mfkiwl/HF-PA-v7/datasheets/irf510-pinout-equivalent.gif

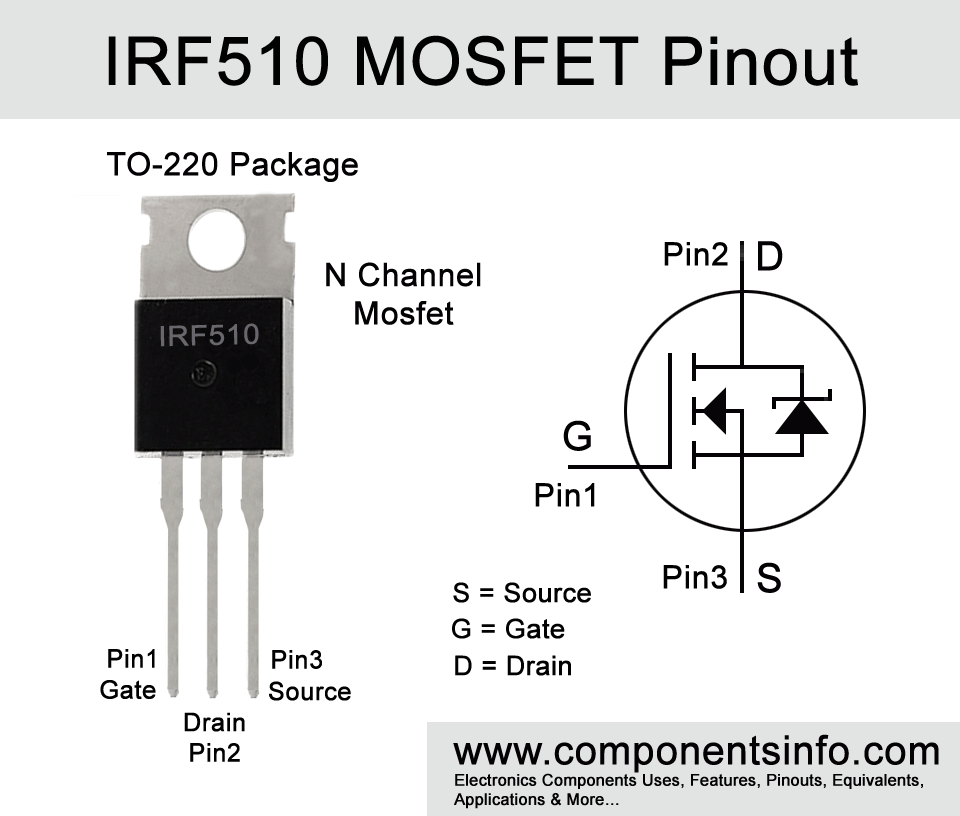
datasheets/irf510-pinout-equivalent.gif
