mfkiwl/HF-PA-v7/datasheets/rd16hhf1-pout-vs-pin.png

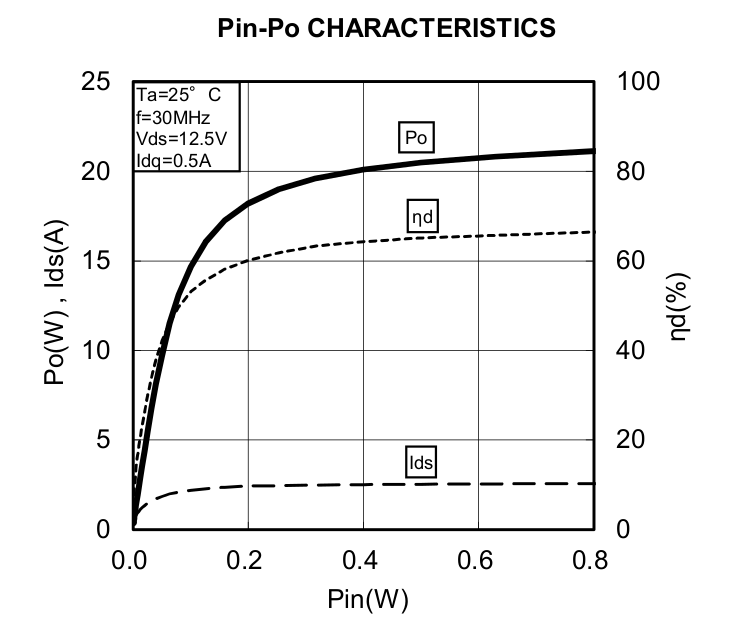
datasheets/rd16hhf1-pout-vs-pin.png
