mfkiwl/HF-PA-v7/Info/15-02-2021-11-58-602a61e1a4f83.jpeg

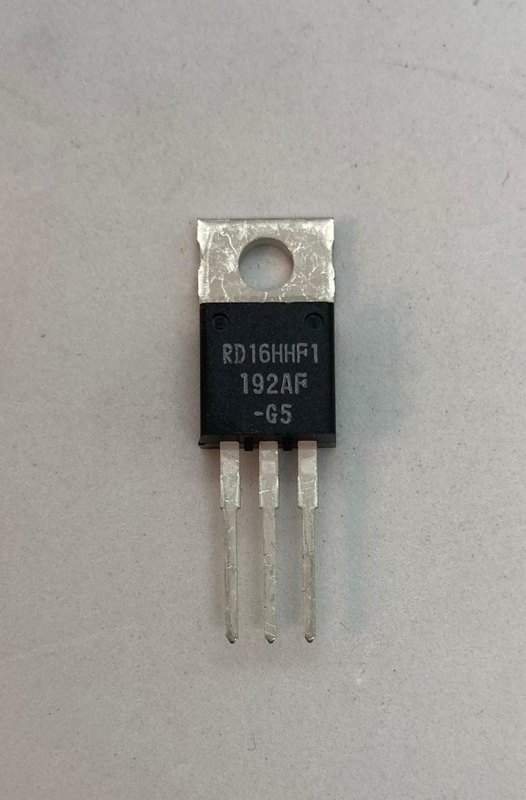
Info/15-02-2021-11-58-602a61e1a4f83.jpeg
