mfkiwl/HF-PA-v7/Info/28M5Wamp1.png

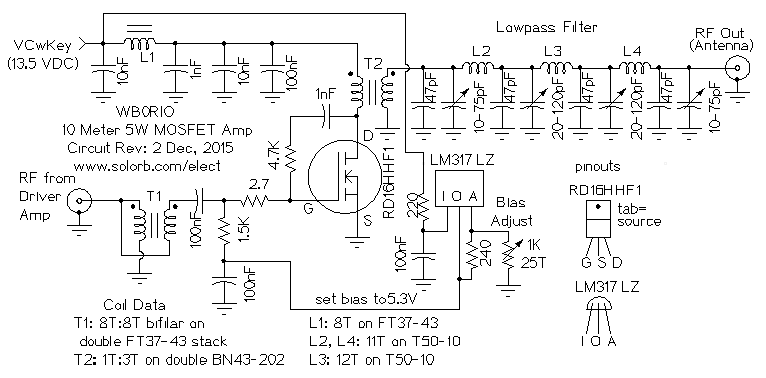
Info/28M5Wamp1.png
