mfkiwl/HF-PA-v7/Info/1367.jpg

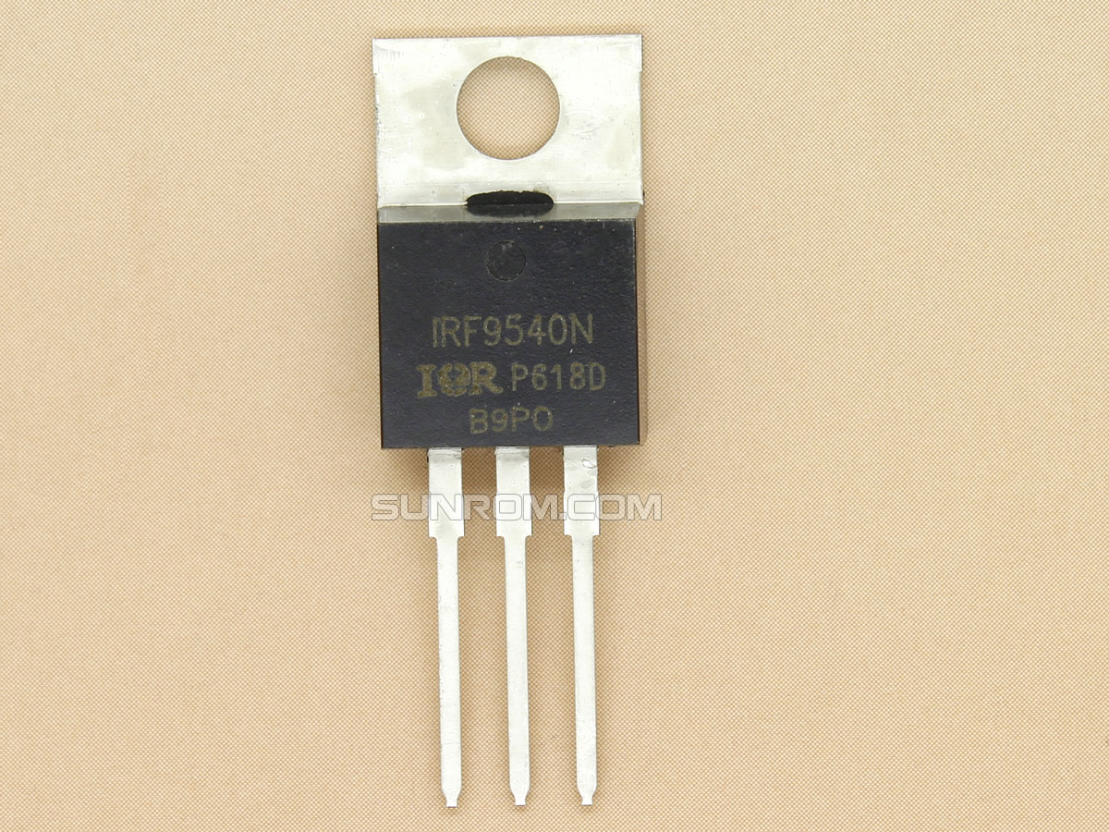
Info/1367.jpg
