mfkiwl/HF-PA-v7/Info/ MTR5B PA.png

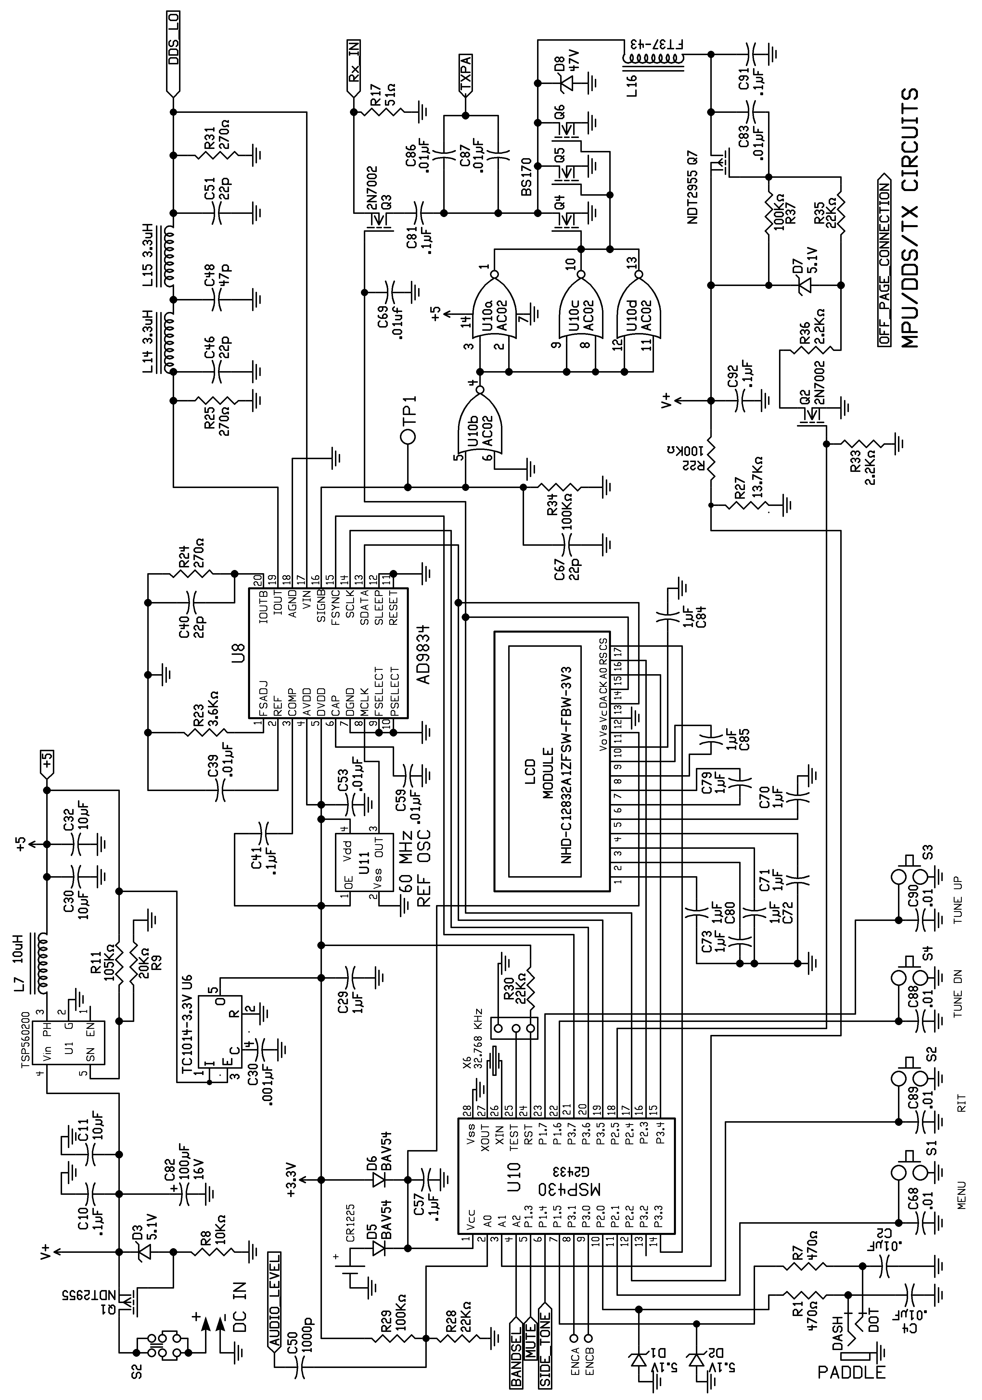
Info/ MTR5B PA.png
