mfkiwl/HF-PA-v7/Info/Hex-Inverter-As-MOSFET-Driver.png

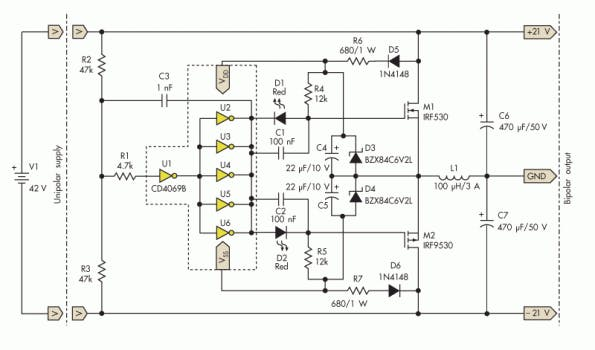
Info/Hex-Inverter-As-MOSFET-Driver.png
