mfkiwl/HF-PA-v7/Info/PFR-3-TX.png

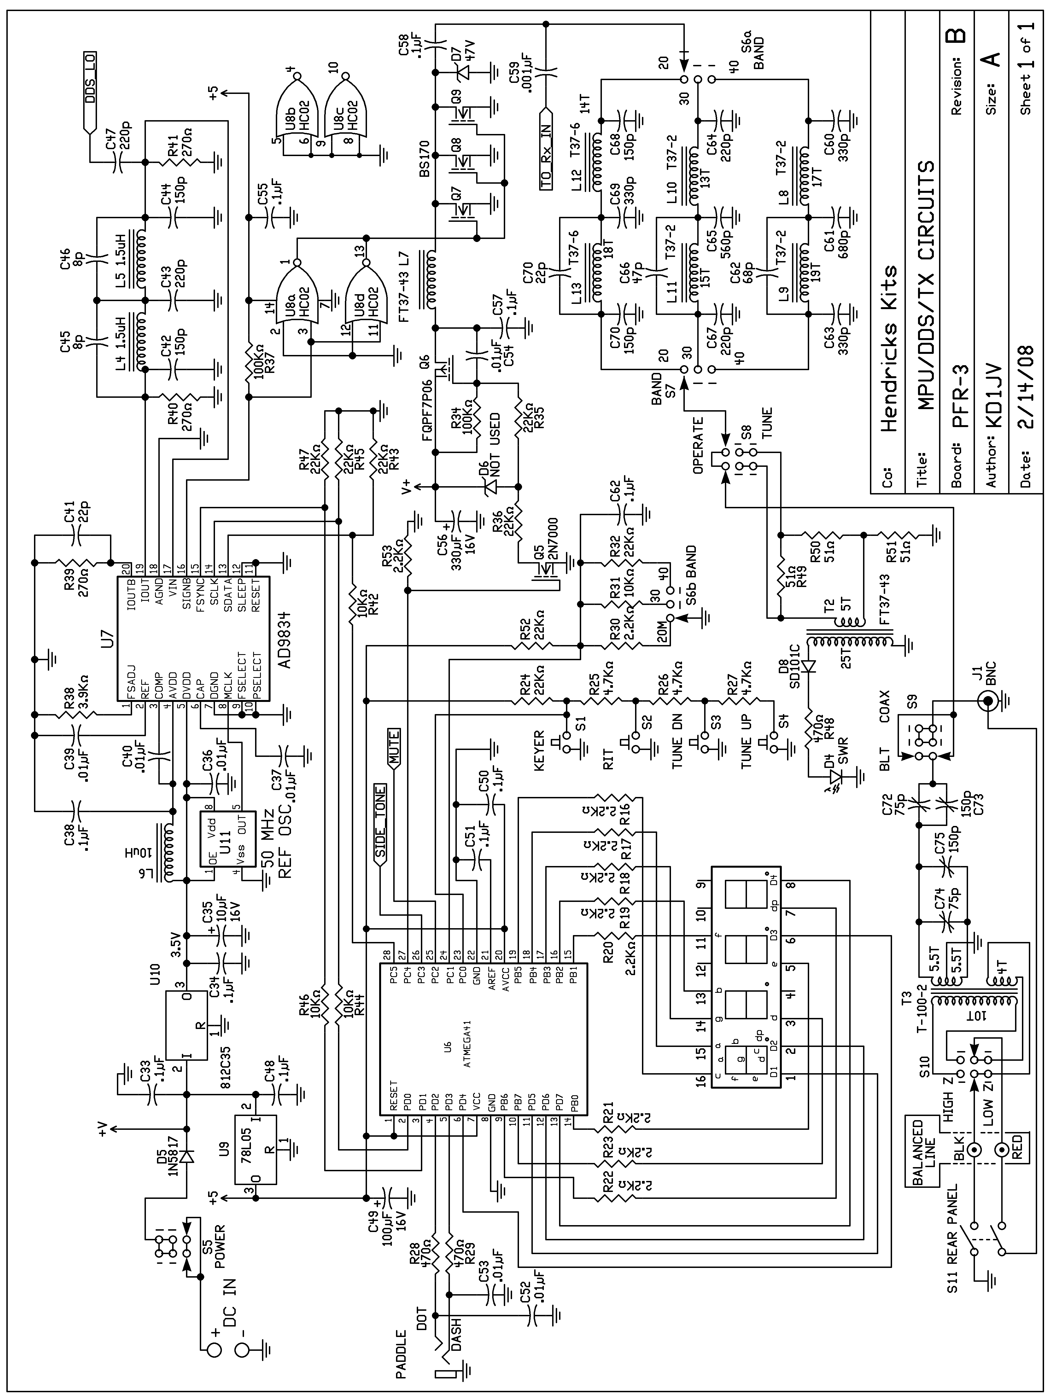
Info/PFR-3-TX.png
