mfkiwl/HF-PA-v7/Info/RD16HHF1-Fake-Screenshot_2022-01-23_14-38-44.png

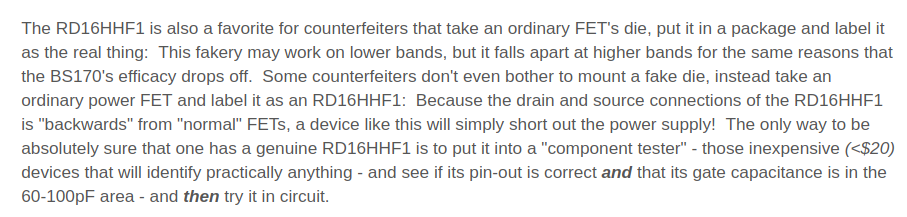
Info/RD16HHF1-Fake-Screenshot_2022-01-23_14-38-44.png
