mfkiwl/HF-PA-v7/Info/Stability-1-ARRL-Chapter-17-2019.png

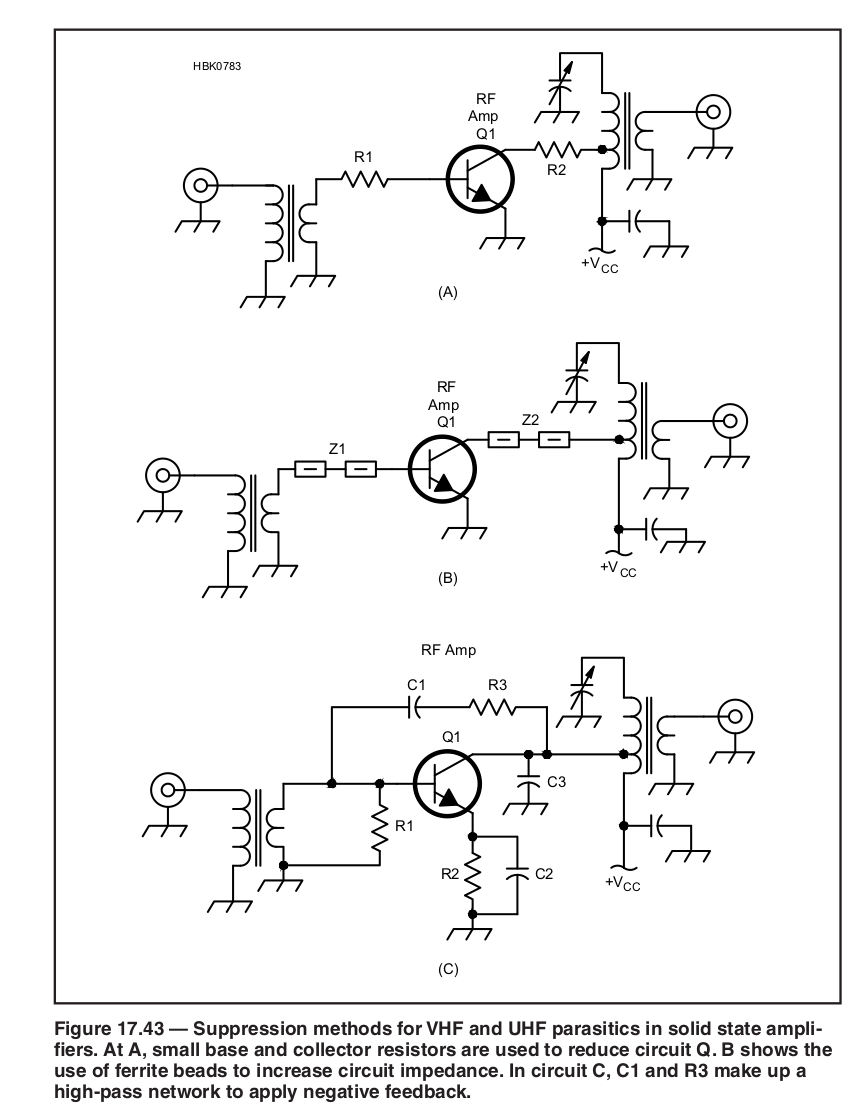
Info/Stability-1-ARRL-Chapter-17-2019.png
