mfkiwl/HF-PA-v7/Wider-LPF/Screenshot_2022-02-07_11-43-11.png

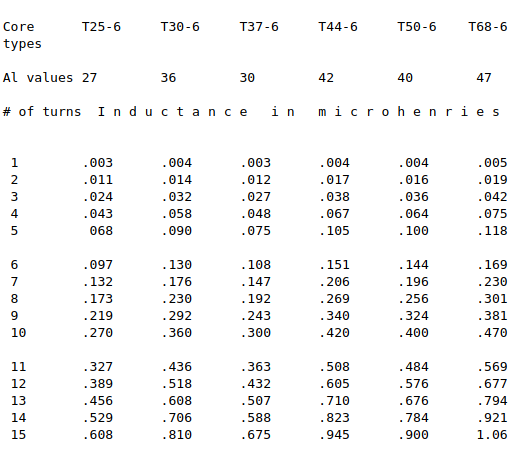
Wider-LPF/Screenshot_2022-02-07_11-43-11.png
