mfkiwl/HF-PA-v7/Wider-LPF/Screenshot_2022-02-07_11-49-57.png

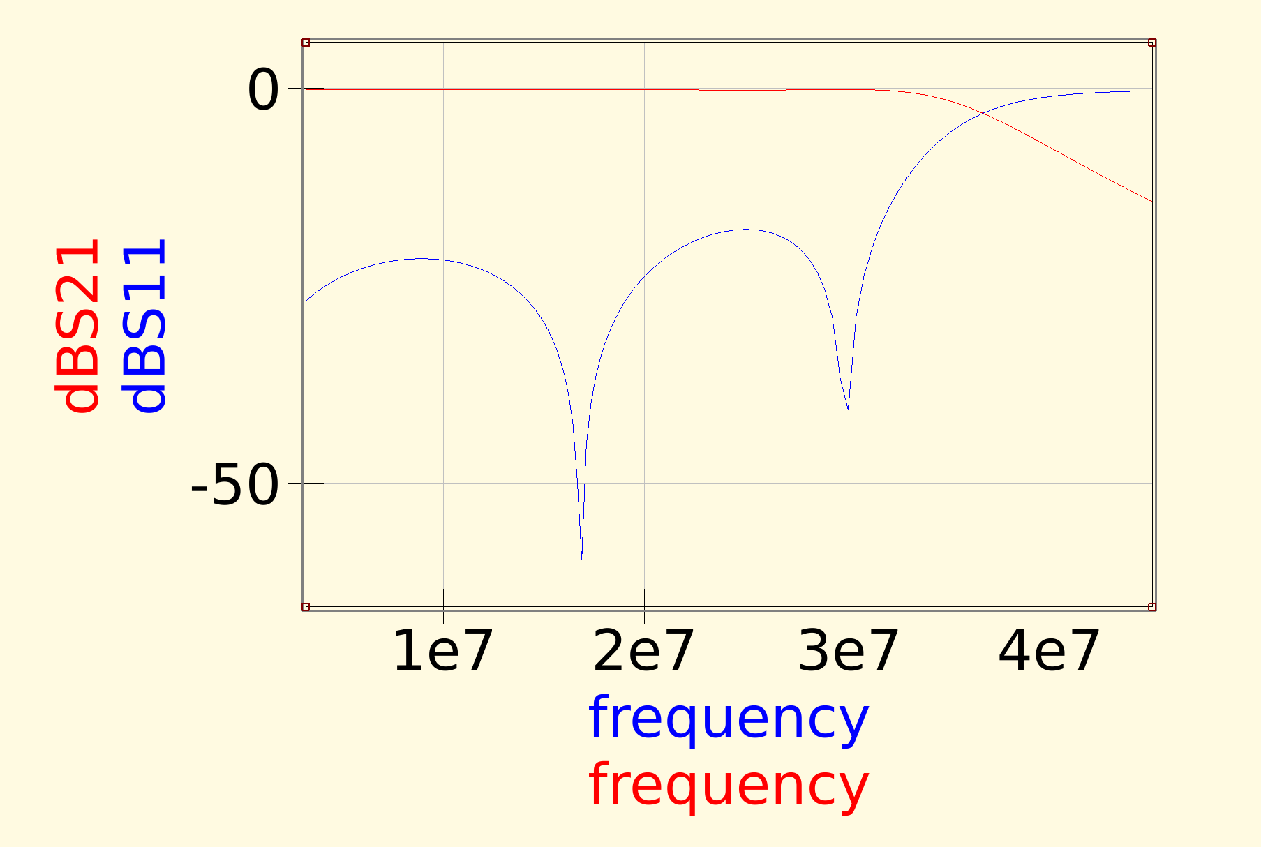
Wider-LPF/Screenshot_2022-02-07_11-49-57.png
