mfkiwl/HF-PA-v7/Info/RD(xy) test from John.jpeg

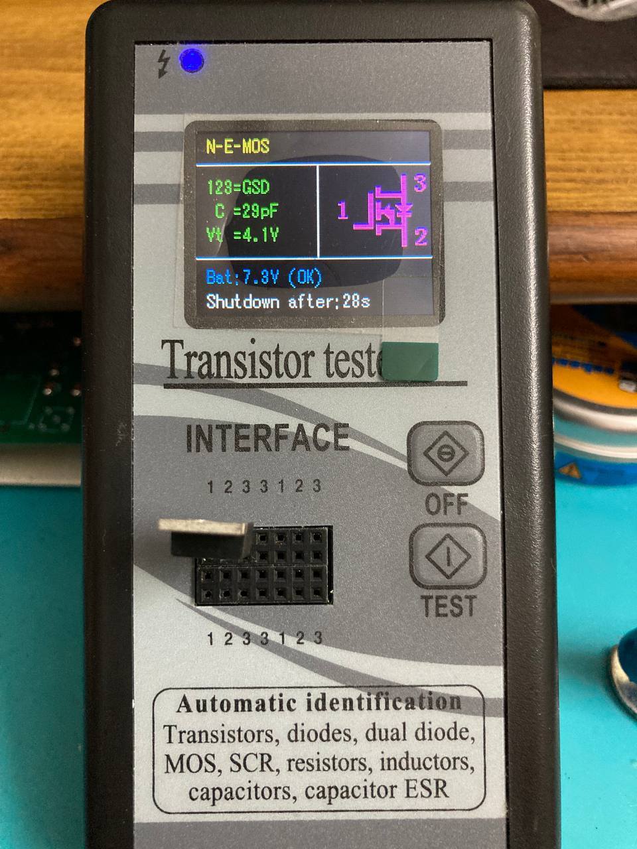
Info/RD(xy) test from John.jpeg
