mfkiwl/HF-PA-v7/HF-PA-Simulations/Driver-Simulation.asc

C1: cap; 100nF
R3: res; 50
V1: voltage; PULSE(0 6 0 0.1p 0.1p 10ns 20ns)
V2: voltage; 13.8
V3: voltage; 6
V4: voltage; 0
Named nets: W1, 0, Vp, Vb, Vz
.tran 200us
.include RD16HHF1.txt
