mfkiwl/HF-PA-v7/HF-PA-Simulations/HF-PA-v1-Simulation-14-MHz-v8-Class-D-RD16HHF1.asc

C1: cap; 10nF
C2: cap; 100nF
L1: ind; 5.6µH
M1: nmos; RD16HHF1
R1: res; 3.3k
R2: res; 4.7
R3: res; 50
RV1: res; 1k
V1: voltage; PULSE(0 6 0 0.1p 0.1p 35.5ns 71ns)
V2: voltage; 13.8
V3: voltage; 6
V4: voltage; 0
Named nets: W1, Vp, 0, Vb, Vz
.tran 20us
.include RD16HHF1.txt
